AidenBTTU/PCB-Design/MotorDriverV1/HBridgeSim.asc

L1: ind; 150µ; Rser=15
M1: nmos; irlz44n
M3: pmos; irf4905
M5: nmos; irlz44n
M6: pmos; irf4905
M7: nmos; irlz44n
M8: nmos; irlz44n
R1: res; 100k
R2: res; 100k
R3: res; 0.5
R4: res; 100k
R5: res; 100k
R6: res; 1k
R7: res; 5k
R8: res; 100k
U1: opamp2; LM324
V1: voltage; 9.6
V2: voltage; PULSE(0 3.3 0 10n 10n 0.9m 1m 8000)
Named nets: 0, Vdd, signal, signal2
.include irf4905.spi
.include irlz44n.spi
.tran 100m
.meas Pavg AVG(V(N003,N004)*I(L1))
.meas Vavg AVG(V(N003,N004))
.include LM324.sub
This file is an example simulation of one side of the H bridge. A 9.6V battery is used
while one signal pin is PWM'd at 90% 1khz and the other signal pin is left open. 
Libraries for the LM324, IRF4905, and IRLZ44N are needed.
